akosbrachna/coil_winder/config4.h

#pragma config FOSC = HS  //HS with PLL enabled used by CPU and USB
#pragma config PLLDIV = 1  //PLL prescaler 20/5=4 MHz (96MHz PLL needs
#pragma config CPUDIV = OSC1_PLL2
#pragma config USBDIV = 2  
#pragma config IESO = OFF
#pragma config PWRT = OFF
#pragma config BOR = OFF
#pragma config BORV = 2
#pragma config VREGEN = ON
#pragma config WDT = OFF
#pragma config WDTPS = 32768
#pragma config MCLRE = ON
#pragma config LPT1OSC = OFF
#pragma config PBADEN = OFF
#pragma config CCP2MX = ON
#pragma config STVREN = ON
#pragma config LVP = OFF
//#pragma config ICPRT = OFF
#pragma config XINST = OFF
#pragma config DEBUG = OFF
#pragma config CP0 = OFF
#pragma config CP1 = OFF
#pragma config CP2 = OFF
#pragma config CPB = OFF
#pragma config CPD = OFF
#pragma config WRT0 = OFF
#pragma config WRT1 = OFF
#pragma config WRT2 = OFF
#pragma config WRT3 = OFF
#pragma config WRTB = OFF
#pragma config WRTC = OFF
#pragma config WRTD = OFF
#pragma config EBTR0 = OFF
#pragma config EBTR1 = OFF
#pragma config EBTR2 = OFF
#pragma config EBTRB = OFF
